o7-machinehum/ovrdrive/config/setting1.png

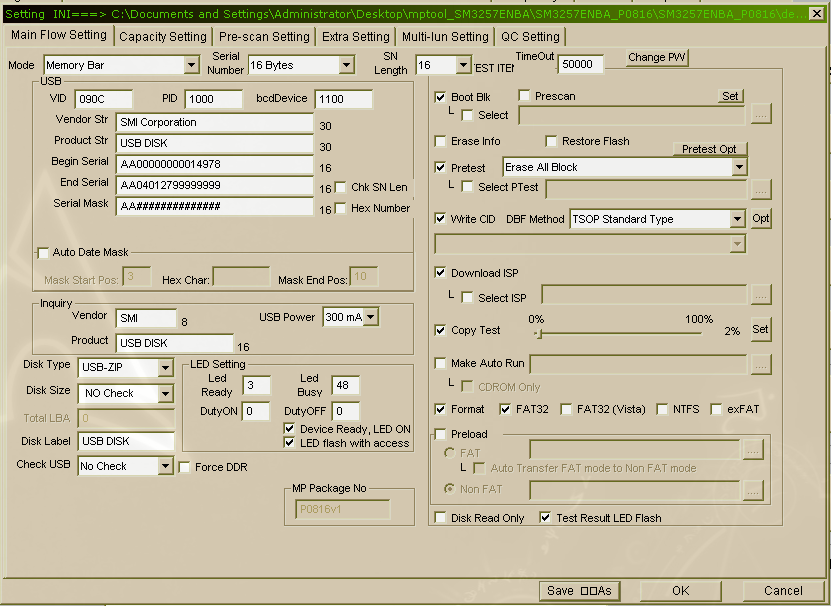
config/setting1.png
