o7-machinehum/ovrdrive/config/setting2.png

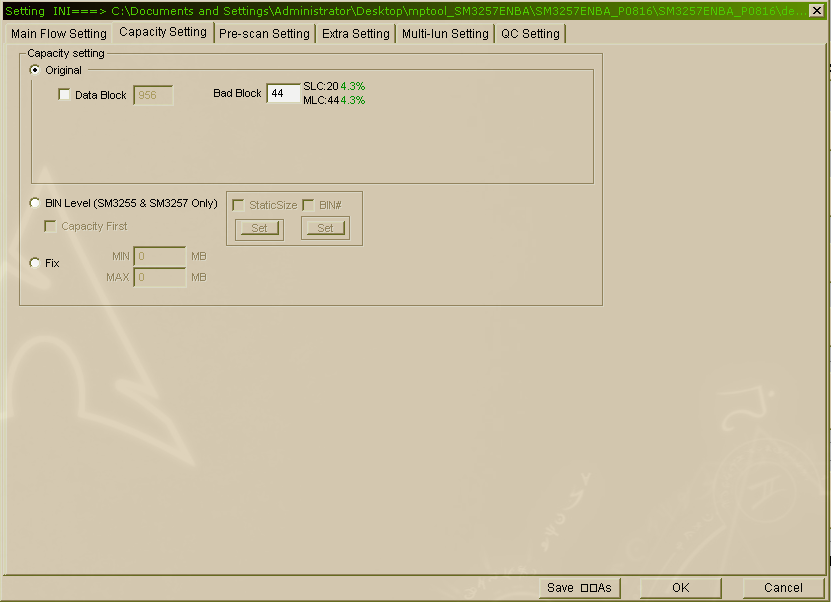
config/setting2.png
