o7-machinehum/ovrdrive/config/setting3.png

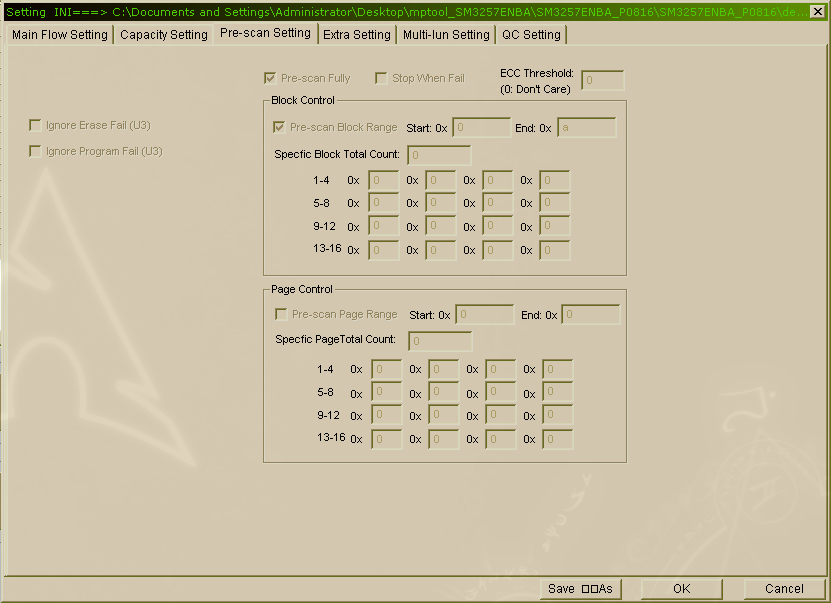
config/setting3.png
