o7-machinehum/ovrdrive/config/setting4.png

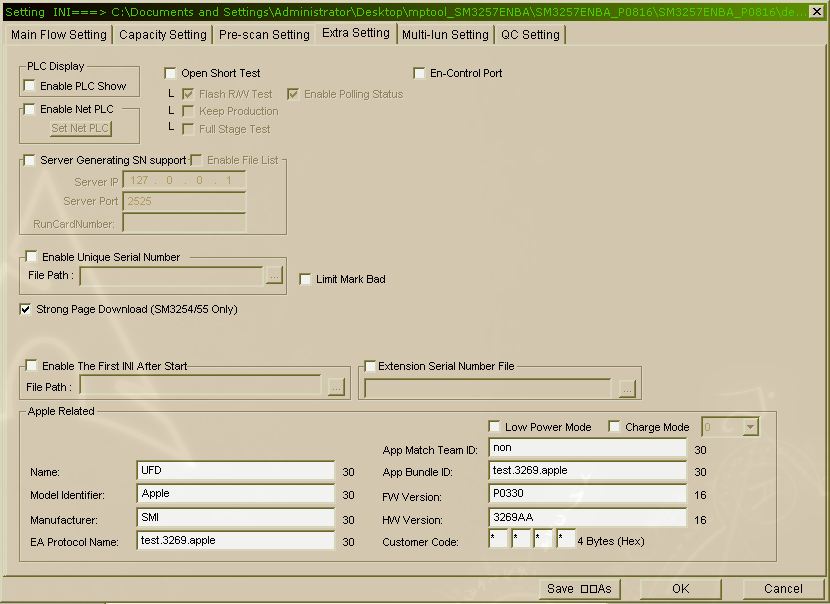
config/setting4.png
