o7-machinehum/ovrdrive/config/setting5.png

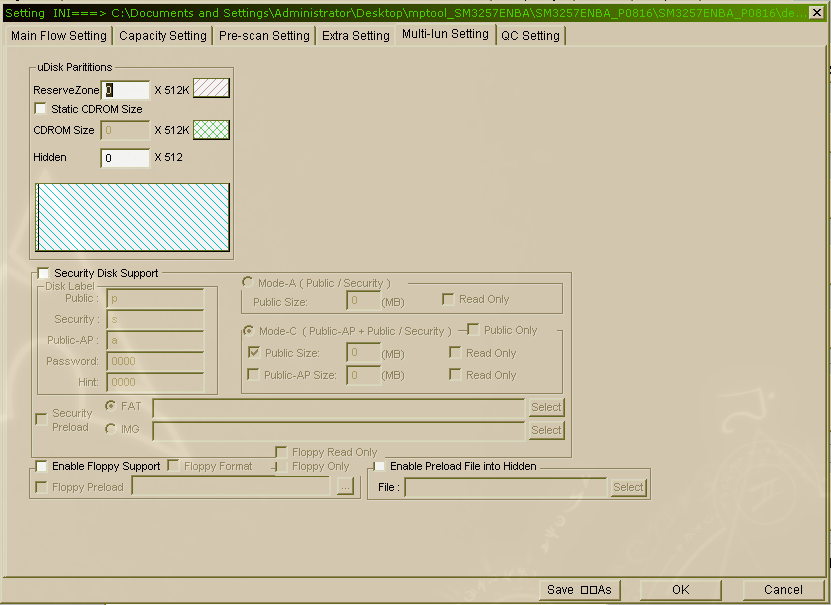
config/setting5.png
