o7-machinehum/ovrdrive/config/setting6.png

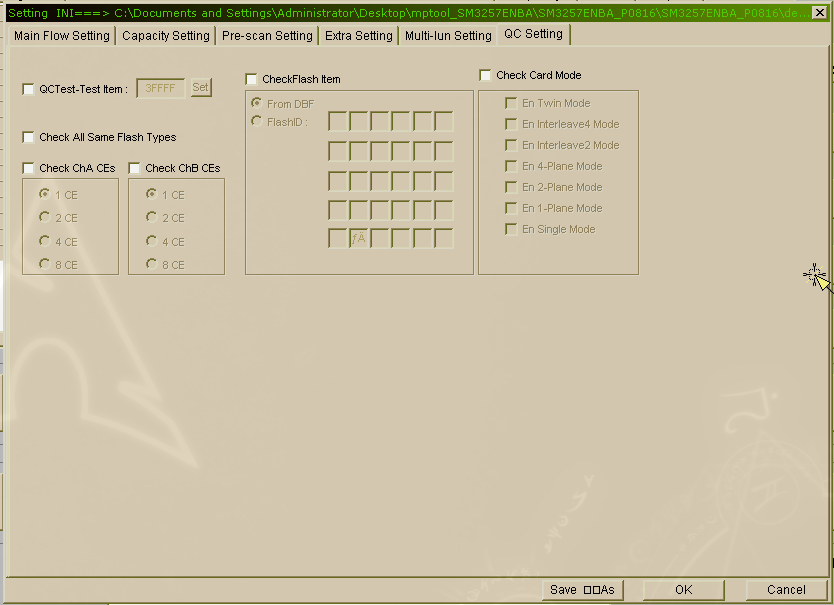
config/setting6.png
