o7-machinehum/ovrdrive/img/drive.png

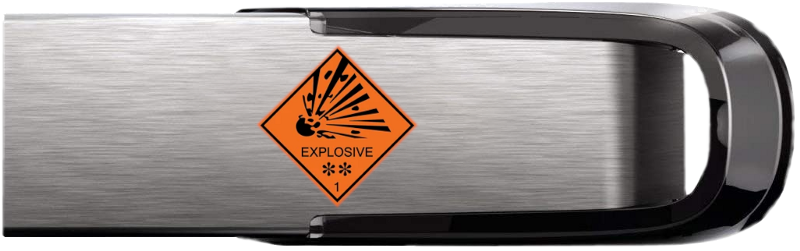
img/drive.png
