o7-machinehum/ovrdrive/img/usb.png

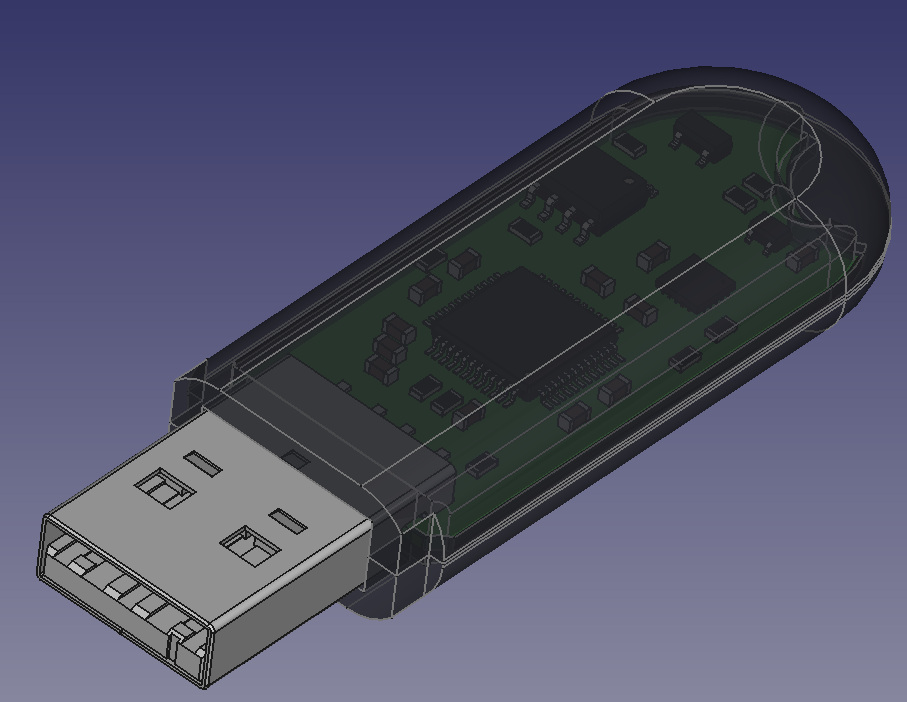
img/usb.png
