o7-machinehum/ovrdrive/testing/thermal/19700101/IMG000015.jpeg

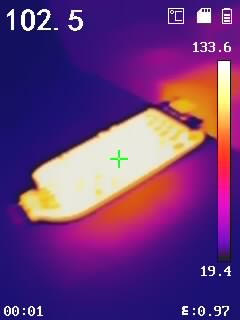
testing/thermal/19700101/IMG000015.jpeg
