o7-machinehum/ovrdrive/testing/thermal/19700101/IMG000019.jpeg

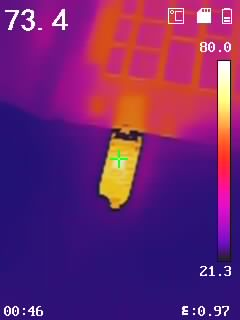
testing/thermal/19700101/IMG000019.jpeg
