o7-machinehum/ovrdrive/sims/desc.asc

C1: cap; 22µF
C2: cap; 22µF
C3: cap; 100nF
D2: diode
D3: diode
M1: nmos; Si1555DL_N
M3: pmos; FDS6875
R1: res; 1k
R2: res; 1R
R3: res; 1k
V1: voltage; 3.3
V2: voltage; 5
V3: voltage; 10
V4: voltage; PULSE(0 5 0 1n 1n 100u 200u 10000)
V5: voltage; PULSE(0 5 200m 1n 1n 10m 20m 1)
Named nets: 3.3V, 5V, 10V, 0
.tran 0 1 0
