o7-machinehum/ovrdrive/sims/Draft1.asc

C1: cap; 100µF; V=25
L1: ind; 10µH
M1: nmos; AON6236
M2: pmos; AONR21307
M3: pmos; BSS84
M4: nmos; BSS123
Q1: npn; 2N3904
R1: res; 100R
R2: res; 100R
R3: res; 100R
R4: res; 100R
V1: voltage; 16
V2: voltage; 3.3
V3: voltage; PULSE(0 3.3 0 1n 1n 1u 2u 1000)
Named nets: 0, 16V, 3.3V, Vout
fc = 1/(pi*sqrt(L*C))
.tran 0 0.003 0
