o7-machinehum/ovrdrive/ee/sims/chargepump.asc

C1: cap; 1µF
C2: cap; 1µF
D1: diode
D2: diode
M1: nmos; IPD600N25N3
R1: res; 1R
V1: voltage; 5
V2: voltage; PULSE(0 5 0 1u 1u 0.000002 0.000002 100)
V3: voltage; PULSE(0 5 500u 1u 1u 1 0.000002 1)
Named nets: 0
.tran 0 0.1 0
